austinscreations/oxrs-security-module/rev 2_1/security I2CRJ45 210 bottom.jpg

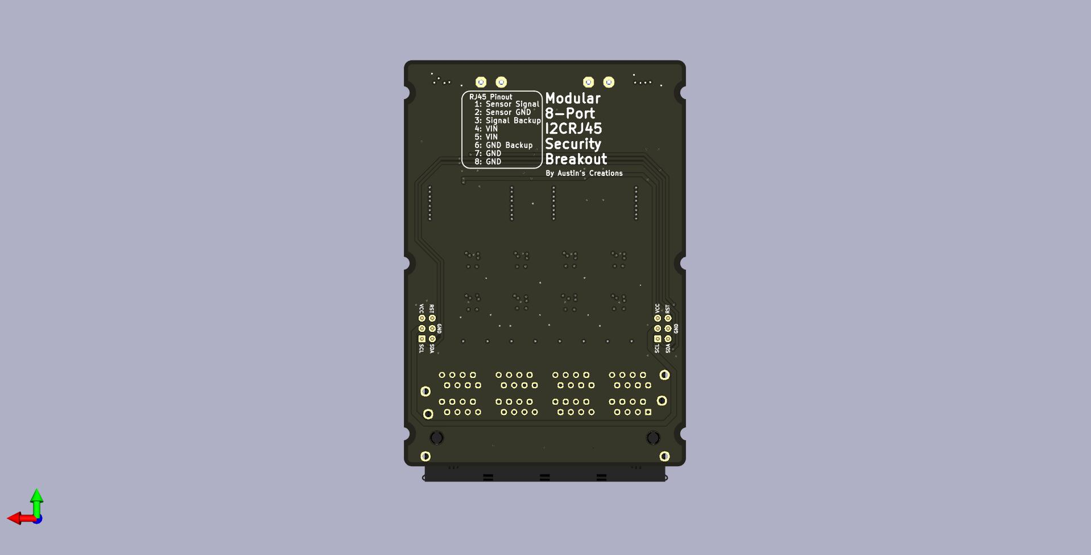
rev 2_1/security I2CRJ45 210 bottom.jpg
