austinscreations/oxrs-security-module/sense breakout/sense breakout top.jpg

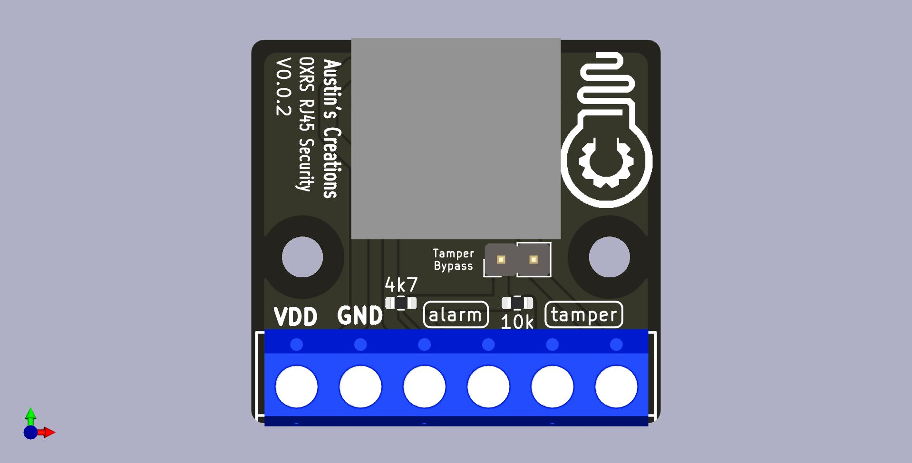
sense breakout/sense breakout top.jpg
